triakshasingh/TPS54331_Buck_Converter/sim/TPS54331_5V_3A_Buck.asc

C1: cap; 4.7µF
C2: cap; 4.7µF
C3: Cap; 0.1µF
C4: Cap; 0.1µF
C5: Cap; 47µF
C6: Cap; 47µF
C7: Cap; 1pF
C8: Cap; 1000pF
C9: Cap; 47pF
D1: schottky; MBRS340
L1: ind; 6.8µH
R1: Res; 10.2k
R2: Res; 1.96k
R3: Res; 29.4k
RLOAD: Res; 1.67
V1: voltage; PWL(0 0 100u 12 2m 12)
X1: TPS54331_TRANS
Named nets: 0, VOUT
.tran 0 20m 0 5u
.model MBRS340 D(Is=20u Rs=0.02 N=1.0 Cjo=500p M=0.5 Eg=0.69 Bv=40 Ibv=1m)
.model MBR340 D(Is=1e-6 Rs=0.02 N=1.0 Cjo=100p Tt=50n Bv=40 Ibv=1e-4)
.meas TRAN vout_final FIND V(vout) AT=3m
.include TPS54331_TRANS.LIB
.options trtol=1 cshunt=1e-12 gmin=1e-10
